Nemanja5199/Hack-PC/Hack/output_files/stp1.jpg

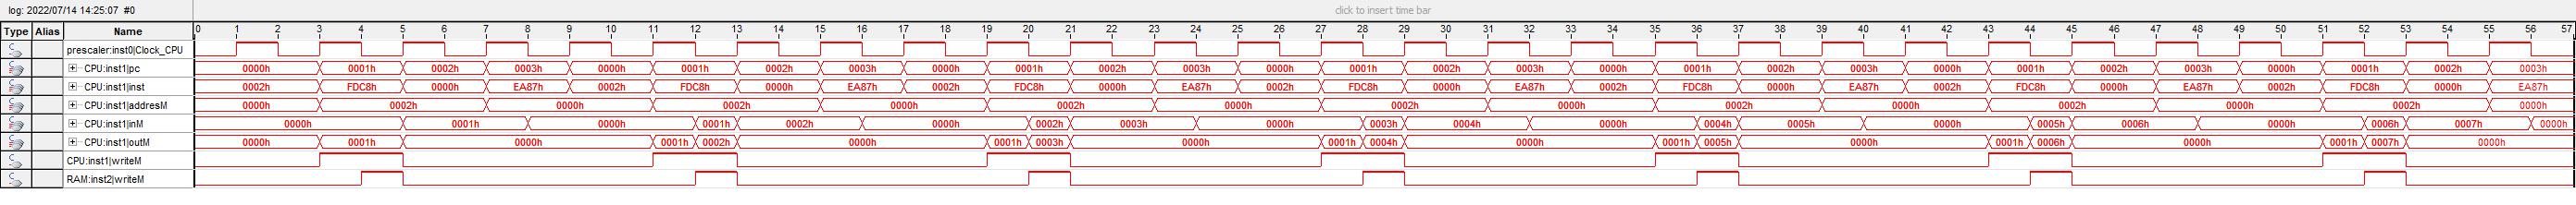
Hack/output_files/stp1.jpg
